koszozoltan/HGA22/docs/20260207_133258.jpg

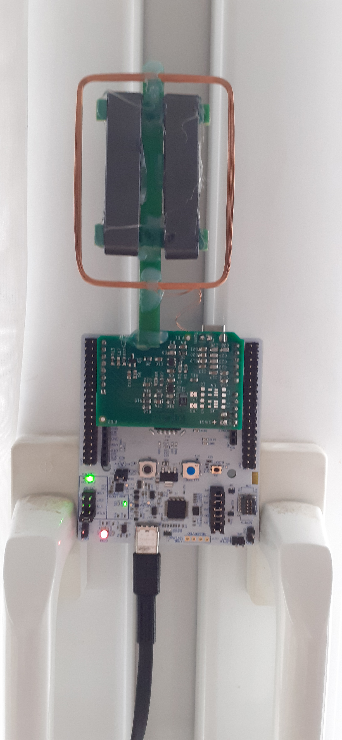
docs/20260207_133258.jpg
