koszozoltan/HGA22/docs/20260227_095823.jpg

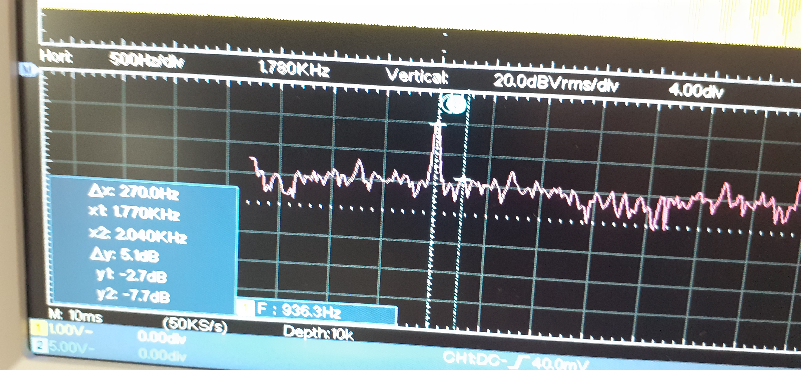
docs/20260227_095823.jpg
