koszozoltan/HGA22/docs/20260227_095835.jpg

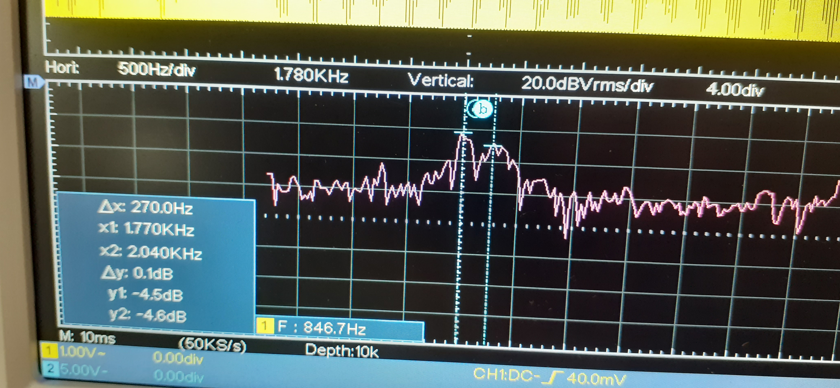
docs/20260227_095835.jpg
