koszozoltan/HGA22/docs/20260306_155042.jpg

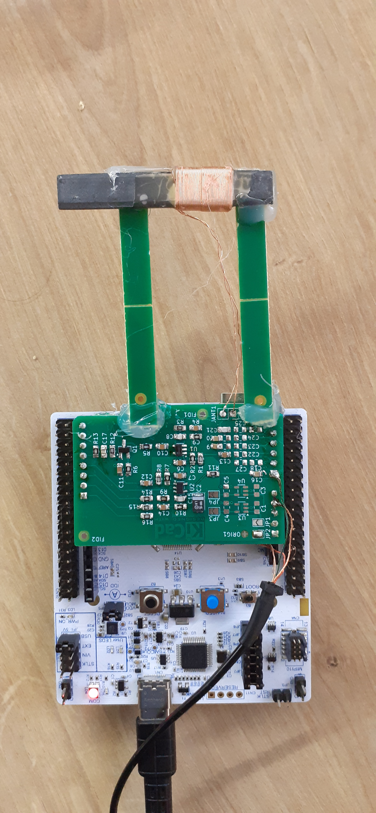
docs/20260306_155042.jpg
