koszozoltan/HGA22/hardware/v1.0/ltspice/HGA22_LM321LV_V2.asc

A1: modulate; mark=135.43kHz; space=135.77kHz
C1: cap; 4.2n
C2: cap; 100p
C3: cap; 100n
C4: cap; 100n
C5: cap; 100n
C6: cap; 100n
C7: cap; 100n
C8: cap; 100µ
C9: cap; 10p
C10: cap; 1n
C11: cap; 1n
C13: cap; 100n
L1: ind2; 320µ
L2: ind2; 320µ; Rser=0.1
M1: nmos; BSS138
R1: res; 1Meg
R2: res; 1Meg
R3: res; 1Meg
R4: res; 100
R5: res; 10G
R6: res; 1Meg
R7: res; 1k
R8: res; 10G
R9: res; 1Meg
R10: res; 100
R11: res; 1k
R12: res; 330k
R13: res; 100
R14: res; 1G
R15: res; 1k
R16: res; 1k
R17: res; 100k
U1: opamp2; LM321LV
U2: opamp2; LM321LV
V1: voltage; PULSE(0 1 0 10n 10n 5m 10m 3)
V2: voltage; PULSE(0 1 0 10n 10n 20m 30m 1)
V3: voltage; 5
V4: voltage; PULSE(0 3.3 0 30n 30n 3.5u 7.3u); Rser=10 Cpar=3p
Named nets: 0, A0
.tran 0 30m 0 10u
K L1 L2 0.00001
.inc LM321LV.cir
PULSE(0 3.3 0 30n 30n 3.5u 7.3u)
