koszozoltan/HGA22/firmware/v1.0/Sources/adc.c

/*
 * adc.c
 *
 *  Created on: Mar 5, 2026
 *      Author: development
 */

/* Includes ------------------------------------------------------------------*/

#include <string.h>
#include <math.h>
#include "util.h"
#include "queue.h"

#include "ringbuffer.h"
#include "tcp_server.h"
#include "arm_math.h"
#include "main.h"
#include "adc.h"




  #define ADC_CALIBRATION_TIMEOUT_MS       (   1UL)
  #define ADC_ENABLE_TIMEOUT_MS            (   1UL)
  #define ADC_DISABLE_TIMEOUT_MS           (   1UL)
  #define ADC_STOP_CONVERSION_TIMEOUT_MS   (   1UL)
  #define ADC_CONVERSION_TIMEOUT_MS        (4000UL)

  /* (CPU clock / ADC clock) is above 32.                                     */
  #define ADC_DELAY_CALIB_ENABLE_CPU_CYCLES  (LL_ADC_DELAY_CALIB_ENABLE_ADC_CYCLES * 32)

  /* supply Vdda (unit: mV).                                                  */
  #define VDDA_APPLI                       (3300UL)

  /* Init variable out of expected ADC conversion data range */
  #define VAR_CONVERTED_DATA_INIT_VALUE    (__LL_ADC_DIGITAL_SCALE(LL_ADC_RESOLUTION_12B) + 1)


  /* Time base range frequency maximum (unit: Hz).*/
  /* With a timer 16 bits, minimum frequency will be 1/32000 times this value.*/
  #define TIMER_FREQUENCY_RANGE_MAX_HZ    (32000UL)



__IO uint16_t uhADCxConvertedData[ADC_CONVERTED_DATA_BUFFER_SIZE];
__IO uint8_t ubDmaTransferStatus = 2U; /* Variable set into DMA interruption callback */
__IO uint8_t ubDmaTransferCnt= 0; /* Variable set into DMA interruption callback */

extern stream_q_t q_signal;

void ADC_Init(void) {

  uint32_t tmp_index;
/* Initialize ADC group regular data buffer values */
  for (tmp_index = 0; tmp_index < ADC_CONVERTED_DATA_BUFFER_SIZE; tmp_index++)
  {
    uhADCxConvertedData[tmp_index] = VAR_CONVERTED_DATA_INIT_VALUE;
  }

  /* USER CODE END 1 */

  /* MCU Configuration--------------------------------------------------------*/

  /* Reset of all peripherals, Initializes the Flash interface and the Systick. */
  LL_APB2_GRP1_EnableClock(LL_APB2_GRP1_PERIPH_SYSCFG);
  LL_APB1_GRP1_EnableClock(LL_APB1_GRP1_PERIPH_PWR);

  /* SysTick_IRQn interrupt configuration */
  NVIC_SetPriority(SysTick_IRQn, 3);


  /* Initialize all configured peripherals */
   //MX_GPIO_Init();
   MX_DMA_Init();
   MX_ADC1_Init();
   MX_TIM1_Init();
   /* USER CODE BEGIN 2 */

   /* Activate ADC */
   /* Perform ADC activation procedure to make it ready to convert. */
   ADC_Activate();

   /* Start ADC group regular conversion */
   /* Note: ADC conversion will effectively start at timer trigger event */
   /* Note: Hardware constraint (refer to description of the functions         */
   /*       below):                                                            */
   /*       On this STM32 series, setting of this feature is conditioned to    */
   /*       ADC state:                                                         */
   /*       ADC must be enabled without conversion on going on group regular,  */
   /*       without ADC disable command on going.                              */
   /* Note: In this example, all these checks are not necessary but are        */
   /*       implemented anyway to show the best practice usages                */
   /*       corresponding to reference manual procedure.                       */
   /*       Software can be optimized by removing some of these checks, if     */
   /*       they are not relevant considering previous settings and actions    */
   /*       in user application.                                               */
   if ((LL_ADC_IsEnabled(ADC1) == 1)               &&
       (LL_ADC_IsDisableOngoing(ADC1) == 0)        &&
       (LL_ADC_REG_IsConversionOngoing(ADC1) == 0)   )
   {
     LL_ADC_REG_StartConversion(ADC1);
   }
   else
   {
     /* Error: ADC conversion start could not be performed */
     Error_Handler();
   }

   /* Start time base */
   LL_TIM_EnableCounter(TIM1);


}


/**
  * @brief ADC1 Initialization Function
  * @param None
  * @retval None
  */
void MX_ADC1_Init(void) {

  LL_ADC_InitTypeDef ADC_InitStruct = {0};
  LL_ADC_REG_InitTypeDef ADC_REG_InitStruct = {0};

  LL_GPIO_InitTypeDef GPIO_InitStruct = {0};

  LL_RCC_SetADCClockSource(LL_RCC_ADC_CLKSOURCE_SYSCLK);

  /* Peripheral clock enable */
  LL_APB2_GRP1_EnableClock(LL_APB2_GRP1_PERIPH_ADC);

  LL_IOP_GRP1_EnableClock(LL_IOP_GRP1_PERIPH_GPIOA);
  /**ADC1 GPIO Configuration
  PA4   ------> ADC1_IN4
  */
  GPIO_InitStruct.Pin = LL_GPIO_PIN_0;
  GPIO_InitStruct.Mode = LL_GPIO_MODE_ANALOG;
  GPIO_InitStruct.Pull = LL_GPIO_PULL_NO;
  LL_GPIO_Init(GPIOA, &GPIO_InitStruct);

  /* ADC1 DMA Init */

  /* ADC1 Init */
  LL_DMA_SetPeriphRequest(DMA1, LL_DMA_CHANNEL_1, LL_DMAMUX_REQ_ADC1);

  LL_DMA_SetDataTransferDirection(DMA1, LL_DMA_CHANNEL_1, LL_DMA_DIRECTION_PERIPH_TO_MEMORY);

  LL_DMA_SetChannelPriorityLevel(DMA1, LL_DMA_CHANNEL_1, LL_DMA_PRIORITY_LOW);

  LL_DMA_SetMode(DMA1, LL_DMA_CHANNEL_1, LL_DMA_MODE_CIRCULAR);

  LL_DMA_SetPeriphIncMode(DMA1, LL_DMA_CHANNEL_1, LL_DMA_PERIPH_NOINCREMENT);

  LL_DMA_SetMemoryIncMode(DMA1, LL_DMA_CHANNEL_1, LL_DMA_MEMORY_INCREMENT);

  LL_DMA_SetPeriphSize(DMA1, LL_DMA_CHANNEL_1, LL_DMA_PDATAALIGN_HALFWORD);

  LL_DMA_SetMemorySize(DMA1, LL_DMA_CHANNEL_1, LL_DMA_MDATAALIGN_HALFWORD);

  /* ADC1 interrupt Init */
  NVIC_SetPriority(ADC1_IRQn, 0);
  NVIC_EnableIRQ(ADC1_IRQn);

  /* USER CODE BEGIN ADC1_Init 1 */
  /* Set DMA transfer addresses of source and destination */
  LL_DMA_ConfigAddresses(DMA1,
                         LL_DMA_CHANNEL_1,
                         LL_ADC_DMA_GetRegAddr(ADC1, LL_ADC_DMA_REG_REGULAR_DATA),
                         (uint32_t)&uhADCxConvertedData,
                         LL_DMA_DIRECTION_PERIPH_TO_MEMORY);

  /* Set DMA transfer size */
  LL_DMA_SetDataLength(DMA1,
                       LL_DMA_CHANNEL_1,
                       ADC_CONVERTED_DATA_BUFFER_SIZE);

  /* Enable DMA transfer interruption: transfer complete */
  LL_DMA_EnableIT_TC(DMA1,
                     LL_DMA_CHANNEL_1);

  /* Enable DMA transfer interruption: half transfer */
  LL_DMA_EnableIT_HT(DMA1,
                     LL_DMA_CHANNEL_1);

  /* Enable DMA transfer interruption: transfer error */
  LL_DMA_EnableIT_TE(DMA1,
                     LL_DMA_CHANNEL_1);

  /* Enable the DMA transfer */
  LL_DMA_EnableChannel(DMA1,
                       LL_DMA_CHANNEL_1);
  /* USER CODE END ADC1_Init 1 */

  /** Configure the global features of the ADC (Clock, Resolution, Data Alignment and number of conversion)
  */

   #define ADC_CHANNEL_CONF_RDY_TIMEOUT_MS ( 1U)
   #if (USE_TIMEOUT == 1)
   uint32_t Timeout ; /* Variable used for Timeout management */
   #endif /* USE_TIMEOUT */

  ADC_InitStruct.Clock = LL_ADC_CLOCK_SYNC_PCLK_DIV4;

  ADC_InitStruct.Resolution = LL_ADC_RESOLUTION_12B;
  ADC_InitStruct.DataAlignment = LL_ADC_DATA_ALIGN_RIGHT;
  ADC_InitStruct.LowPowerMode = LL_ADC_LP_MODE_NONE;
  LL_ADC_Init(ADC1, &ADC_InitStruct);
  LL_ADC_REG_SetSequencerConfigurable(ADC1, LL_ADC_REG_SEQ_FIXED);
  ADC_REG_InitStruct.TriggerSource = LL_ADC_REG_TRIG_EXT_TIM1_TRGO2;
  ADC_REG_InitStruct.SequencerLength = LL_ADC_REG_SEQ_SCAN_DISABLE;
  ADC_REG_InitStruct.SequencerDiscont = LL_ADC_REG_SEQ_DISCONT_DISABLE;
  ADC_REG_InitStruct.ContinuousMode = LL_ADC_REG_CONV_SINGLE;
  ADC_REG_InitStruct.DMATransfer = LL_ADC_REG_DMA_TRANSFER_UNLIMITED;
  ADC_REG_InitStruct.Overrun = LL_ADC_REG_OVR_DATA_OVERWRITTEN;
  LL_ADC_REG_Init(ADC1, &ADC_REG_InitStruct);
  LL_ADC_REG_SetSequencerScanDirection(ADC1, LL_ADC_REG_SEQ_SCAN_DIR_FORWARD);
#warning ADC oversample
#if 0
  LL_ADC_SetOverSamplingScope(ADC1, LL_ADC_OVS_DISABLE);
#else
  LL_ADC_SetOverSamplingScope(ADC1, LL_ADC_OVS_GRP_REGULAR_CONTINUED);
   LL_ADC_ConfigOverSamplingRatioShift(ADC1, LL_ADC_OVS_RATIO_32, LL_ADC_OVS_SHIFT_RIGHT_5);
   LL_ADC_SetOverSamplingDiscont(ADC1, LL_ADC_OVS_REG_CONT);
#endif


  LL_ADC_SetTriggerFrequencyMode(ADC1, LL_ADC_CLOCK_FREQ_MODE_HIGH);
  LL_ADC_REG_SetSequencerChAdd(ADC1, LL_ADC_CHANNEL_0);

   /* Poll for ADC channel configuration ready */
   #if (USE_TIMEOUT == 1)
   Timeout = ADC_CHANNEL_CONF_RDY_TIMEOUT_MS;
   #endif /* USE_TIMEOUT */
   while (LL_ADC_IsActiveFlag_CCRDY(ADC1) == 0)
     {
   #if (USE_TIMEOUT == 1)
   /* Check Systick counter flag to decrement the time-out value */
   if (LL_SYSTICK_IsActiveCounterFlag())
     {
   if(Timeout-- == 0)
         {
   Error_Handler();
         }
     }
   #endif /* USE_TIMEOUT */
     }
   /* Clear flag ADC channel configuration ready */
   LL_ADC_ClearFlag_CCRDY(ADC1);
  LL_ADC_REG_SetTriggerEdge(ADC1, LL_ADC_REG_TRIG_EXT_RISING);
#warning ADC oversample
#if 0
  LL_ADC_SetSamplingTimeCommonChannels(ADC1, LL_ADC_SAMPLINGTIME_COMMON_1, LL_ADC_SAMPLINGTIME_79CYCLES_5);
#else
  LL_ADC_SetSamplingTimeCommonChannels(ADC1, LL_ADC_SAMPLINGTIME_COMMON_1, LL_ADC_SAMPLINGTIME_7CYCLES_5);
#endif

  LL_ADC_DisableIT_EOC(ADC1);
  LL_ADC_DisableIT_EOS(ADC1);

   /* Enable ADC internal voltage regulator */
   LL_ADC_EnableInternalRegulator(ADC1);
   /* Delay for ADC internal voltage regulator stabilization. */
   /* Compute number of CPU cycles to wait for, from delay in us. */
   /* Note: Variable divided by 2 to compensate partially */
   /* CPU processing cycles (depends on compilation optimization). */
   /* Note: If system core clock frequency is below 200kHz, wait time */
   /* is only a few CPU processing cycles. */
   uint32_t wait_loop_index;
   wait_loop_index = ((LL_ADC_DELAY_INTERNAL_REGUL_STAB_US * (SystemCoreClock / (100000 * 2))) / 10);
   while(wait_loop_index != 0)
     {
   wait_loop_index--;
     }
  /* USER CODE BEGIN ADC1_Init 2 */

  /* Configuration of ADC interruptions */
  /* Enable interruption ADC group regular overrun */
  LL_ADC_EnableIT_OVR(ADC1);

  /* USER CODE END ADC1_Init 2 */

}

/**
  * @brief TIM1 Initialization Function
  * @param None
  * @retval None
  */
void MX_TIM1_Init(void) {

  /* USER CODE BEGIN TIM1_Init 0 */
  uint32_t tim_prescaler;
  uint32_t tim_period;
  /* USER CODE END TIM1_Init 0 */

  LL_TIM_InitTypeDef TIM_InitStruct = {0};

  /* Peripheral clock enable */
  LL_APB2_GRP1_EnableClock(LL_APB2_GRP1_PERIPH_TIM1);

  /* USER CODE BEGIN TIM1_Init 1 */

  /* Set timer prescaler value (timer frequency) */
  /* Note: Value TIMER_FREQUENCY_RANGE_MAX_HZ with factor 2 to have a minimum
           timer resolution */
  tim_prescaler = __LL_TIM_CALC_PSC(SystemCoreClock, TIMER_FREQUENCY_RANGE_MAX_HZ * 2);

  /* Set timer period value (time base frequency) */
  tim_period = __LL_TIM_CALC_ARR(SystemCoreClock, tim_prescaler, TIMER_FREQUENCY_HZ);

  /* USER CODE END TIM1_Init 1 */
  TIM_InitStruct.Prescaler = tim_prescaler;
  TIM_InitStruct.CounterMode = LL_TIM_COUNTERMODE_UP;
  TIM_InitStruct.Autoreload = tim_period;
  TIM_InitStruct.ClockDivision = LL_TIM_CLOCKDIVISION_DIV1;
  TIM_InitStruct.RepetitionCounter = 0;
  LL_TIM_Init(TIM1, &TIM_InitStruct);
  LL_TIM_DisableARRPreload(TIM1);
  LL_TIM_SetClockSource(TIM1, LL_TIM_CLOCKSOURCE_INTERNAL);
  LL_TIM_SetTriggerOutput(TIM1, LL_TIM_TRGO_UPDATE);
  LL_TIM_SetTriggerOutput2(TIM1, LL_TIM_TRGO2_UPDATE);
  LL_TIM_DisableMasterSlaveMode(TIM1);
}

/**
  * Enable DMA controller clock
  */
void MX_DMA_Init(void) {

  /* Init with LL driver */
  /* DMA controller clock enable */
  LL_AHB1_GRP1_EnableClock(LL_AHB1_GRP1_PERIPH_DMA1);

  /* DMA interrupt init */
  /* DMA1_Channel1_IRQn interrupt configuration */
  NVIC_SetPriority(DMA1_Channel1_IRQn, 0);
  NVIC_EnableIRQ(DMA1_Channel1_IRQn);

}

void ADC_Activate(void) {
  __IO uint32_t wait_loop_index = 0U;
  __IO uint32_t backup_setting_adc_dma_transfer = 0U;
  #if (USE_TIMEOUT == 1)
  uint32_t Timeout = 0U; /* Variable used for timeout management */
  #endif /* USE_TIMEOUT */

  /*## Operation on ADC hierarchical scope: ADC instance #####################*/

  /* Note: Hardware constraint (refer to description of the functions         */
  /*       below):                                                            */
  /*       On this STM32 series, setting of these features is conditioned to  */
  /*       ADC state:                                                         */
  /*       ADC must be disabled.                                              */
  /* Note: In this example, all these checks are not necessary but are        */
  /*       implemented anyway to show the best practice usages                */
  /*       corresponding to reference manual procedure.                       */
  /*       Software can be optimized by removing some of these checks, if     */
  /*       they are not relevant considering previous settings and actions    */
  /*       in user application.                                               */
  if (LL_ADC_IsEnabled(ADC1) == 0)
  {
    /* Enable ADC internal voltage regulator */
    LL_ADC_EnableInternalRegulator(ADC1);

    /* Delay for ADC internal voltage regulator stabilization.                */
    /* Compute number of CPU cycles to wait for, from delay in us.            */
    /* Note: Variable divided by 2 to compensate partially                    */
    /*       CPU processing cycles (depends on compilation optimization).     */
    /* Note: If system core clock frequency is below 200kHz, wait time        */
    /*       is only a few CPU processing cycles.                             */
    wait_loop_index = ((LL_ADC_DELAY_INTERNAL_REGUL_STAB_US * (SystemCoreClock / (100000 * 2))) / 10);
    while(wait_loop_index != 0)
    {
      wait_loop_index--;
    }

    /* Disable ADC DMA transfer request during calibration */
    /* Note: Specificity of this STM32 series: Calibration factor is           */
    /*       available in data register and also transferred by DMA.           */
    /*       To not insert ADC calibration factor among ADC conversion data   */
    /*       in DMA destination address, DMA transfer must be disabled during */
    /*       calibration.                                                     */
    backup_setting_adc_dma_transfer = LL_ADC_REG_GetDMATransfer(ADC1);
    LL_ADC_REG_SetDMATransfer(ADC1, LL_ADC_REG_DMA_TRANSFER_NONE);

    /* Run ADC self calibration */
    LL_ADC_StartCalibration(ADC1);

    /* Poll for ADC effectively calibrated */
    #if (USE_TIMEOUT == 1)
    Timeout = ADC_CALIBRATION_TIMEOUT_MS;
    #endif /* USE_TIMEOUT */

    while (LL_ADC_IsCalibrationOnGoing(ADC1) != 0)
    {
    #if (USE_TIMEOUT == 1)
      /* Check Systick counter flag to decrement the time-out value */
      if (LL_SYSTICK_IsActiveCounterFlag())
      {
        if(Timeout-- == 0)
        {
          /* Error: Time-out */
          Error_Handler();
        }
      }
    #endif /* USE_TIMEOUT */
    }

    /* Restore ADC DMA transfer request after calibration */
    LL_ADC_REG_SetDMATransfer(ADC1, backup_setting_adc_dma_transfer);

    /* Delay between ADC end of calibration and ADC enable.                   */
    /* Note: Variable divided by 2 to compensate partially                    */
    /*       CPU processing cycles (depends on compilation optimization).     */
    wait_loop_index = (ADC_DELAY_CALIB_ENABLE_CPU_CYCLES >> 1);
    while(wait_loop_index != 0)
    {
      wait_loop_index--;
    }

    /* Enable ADC */
    LL_ADC_Enable(ADC1);

    /* Poll for ADC ready to convert */
    #if (USE_TIMEOUT == 1)
    Timeout = ADC_ENABLE_TIMEOUT_MS;
    #endif /* USE_TIMEOUT */

    while (LL_ADC_IsActiveFlag_ADRDY(ADC1) == 0)
    {
    #if (USE_TIMEOUT == 1)
      /* Check Systick counter flag to decrement the time-out value */
      if (LL_SYSTICK_IsActiveCounterFlag())
      {
        if(Timeout-- == 0)
        {
          /* Error: Time-out */
          Error_Handler();
        }
      }
    #endif /* USE_TIMEOUT */
    }

    /* Note: ADC flag ADRDY is not cleared here to be able to check ADC       */
    /*       status afterwards.                                               */
    /*       This flag should be cleared at ADC Deactivation, before a new    */
    /*       ADC activation, using function "LL_ADC_ClearFlag_ADRDY()".       */
  }

  /*## Operation on ADC hierarchical scope: ADC group regular ################*/
  /* Note: No operation on ADC group regular performed here.                  */
  /*       ADC group regular conversions to be performed after this function  */
  /*       using function:                                                    */
  /*       "LL_ADC_REG_StartConversion();"                                    */

  /*## Operation on ADC hierarchical scope: ADC group injected ###############*/
  /* Note: Feature not available on this STM32 series */

}


void AdcDmaTransferComplete_Callback() {


	sq_push(&q_signal, (int16_t *)uhADCxConvertedData, ADC_CONVERTED_DATA_BUFFER_SIZE);

	ubDmaTransferStatus = 1;
	ubDmaTransferCnt++;
}


/**
  * @brief  DMA half transfer callback
  * @note   This function is executed when the half transfer interrupt
  *         is generated
  * @retval None
  */
void AdcDmaTransferHalf_Callback() {

}



/**
  * @brief  DMA transfer error callback
  * @note   This function is executed when the transfer error interrupt
  *         is generated during DMA transfer
  * @retval None
  */
void AdcDmaTransferError_Callback() {
  if(ubDmaTransferStatus == 1)
  {
    /* Update status variable of DMA transfer */
    ubDmaTransferStatus = 0;
  }

  /* Error detected during DMA transfer */
  Error_Handler();
}

/**
  * @brief  ADC group regular overrun interruption callback
  * @note   This function is executed when ADC group regular
  *         overrun error occurs.
  * @retval None
  */
void AdcGrpRegularOverrunError_Callback(void) {
  /* Note: Disable ADC interruption that caused this error before entering in
           infinite loop below. */

  /* In case of error due to overrun: Disable ADC group regular overrun interruption */
  LL_ADC_DisableIT_OVR(ADC1);

  /* Error reporting */
  Error_Handler();
}
