koszozoltan/HGA22/firmware/v1.0/Sources/iq.c

#include "main.h"
#include <string.h>
#include "math.h"
#include "iq.h"
#include "util.h"


static const  int16_t sinTable[TABLE_SIZE] = {
0,
201,402,603,804,1005,1206,1407,1607,1808,2009,2210,2410,2611,2811,3011,3211,
3411,3611,3811,4011,4210,4409,4609,4808,5006,5205,5403,5602,5800,5997,6195,6392,
6589,6786,6983,7179,7375,7571,7766,7961,8156,8351,8545,8739,8933,9126,9319,9512,
9704,9896,10087,10278,10469,10659,10849,11039,11228,11416,11605,11793,11980,12167,12353,12539,
12725,12910,13094,13278,13462,13645,13828,14010,14191,14372,14552,14732,14912,15090,15269,15446,
15623,15800,15976,16151,16325,16499,16673,16846,17018,17189,17360,17530,17700,17869,18037,18204,
18371,18537,18703,18868,19032,19195,19358,19519,19681,19841,20001,20159,20318,20475,20631,20787,
20942,21097,21250,21403,21555,21706,21856,22005,22154,22301,22448,22594,22740,22884,23027,23170,
23312,23453,23593,23732,23870,24007,24144,24279,24414,24547,24680,24812,24943,25073,25201,25330,
25457,25583,25708,25832,25955,26077,26199,26319,26438,26557,26674,26790,26905,27020,27133,27245,
27356,27466,27576,27684,27791,27897,28002,28106,28208,28310,28411,28511,28609,28707,28803,28898,
28993,29086,29178,29269,29359,29447,29535,29621,29707,29791,29874,29956,30037,30117,30196,30273,
30350,30425,30499,30572,30644,30714,30784,30852,30919,30985,31050,31114,31176,31237,31298,31357,
31414,31471,31526,31581,31634,31685,31736,31785,31834,31881,31927,31971,32015,32057,32098,32138,
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
    if (x <= -1.0f) return -32768;
    return (int32_t)(x * Q15_SCALE);
}

void iq_st_init(iq_st *iq, uint16_t mixFreq)
{
    iq->phase  = 0;
    iq->i_filt = 0;
    iq->q_filt = 0;
    iq->prev_i = 0;
    iq->prev_q = 0;

    iq->sampleRate = 8000;
    iq->mixFreq    = mixFreq;

    // keresés a táblában
    for (int i = 0; i < (int)(sizeof(mix_table)/sizeof(mix_table[0])); i++)
    {
        if (mix_table[i].freq == mixFreq)
        {
            iq->omega    = mix_table[i].omega_q15;
            iq->lpfAlpha = mix_table[i].alpha_q15;
            return;
        }
    }

    // ha nincs egyezés: safe default
    iq->omega    = 0;
    iq->lpfAlpha = 0;
}


// ---------------------------
//   Sin/Cos táblázat (Q15)
// ---------------------------
void initSinCosTable(void) {
#if 0
    for (int i = 0; i < TABLE_SIZE; i++)
    {
        float angle = (2.0f * PI * i) / TABLE_SIZE;
        sinTable[i] = float_to_q15(sinf(angle));
        cosTable[i] = float_to_q15(cosf(angle));
    }
#endif
}

// ---------------------------
//  Fázis → index (Q15)
//  phase = rad * 32768
// ---------------------------
static inline int phaseToIndex(int32_t phase_q15)
{
    // skála: TABLE_SIZE / (2π)  →  1024 / 6.283185
    // állandó Q15-ben:
    const float scale = (float)TABLE_SIZE / (2.0f * PI);
    int32_t scaled = (int32_t)(phase_q15 / 32768.0f * scale);

    int idx = scaled % TABLE_SIZE;
    if (idx < 0) idx += TABLE_SIZE;
    return idx;
}

// ---------------------------
//       IQ Power Q15
// ---------------------------
int32_t iq_power_q15(int16_t sample, iq_st* st)
{


    int idx = phaseToIndex(st->phase);

    int16_t lo_i = cosTable[idx];
    int16_t lo_q = sinTable[idx];

    // fázis növelés
    st->phase += st->omega;
    static const int32_t FULL_ROT = (int32_t)(2.0f * PI * 32768);
    if (st->phase >= FULL_ROT) st->phase -= FULL_ROT;
    else if (st->phase < 0)   st->phase += FULL_ROT;

    // I/Q keverés: (sample * lo) >> 15
    int32_t i = ( (int32_t)sample * lo_i ) >> 15;
    int32_t q = ( (int32_t)sample * lo_q ) >> 15;

    // LPF: y += α (x − y)
    st->i_filt += ( (int32_t)st->lpfAlpha * (i - st->i_filt) ) >> 15;
    st->q_filt += ( (int32_t)st->lpfAlpha * (q - st->q_filt) ) >> 15;

    // power = I^2 + Q^2   (>>15, hogy normalizált legyen)
    int32_t power =
        ((st->i_filt * st->i_filt) >> 15) +
        ((st->q_filt * st->q_filt) >> 15);

    return power;
}

int16_t scale_to_x15_int(int32_t x, int32_t min, int32_t max, int64_t range ) {
    if (x <= min) return -32768;
    if (x >= max) return 32767;
    int64_t result = (((int64_t)(x - min) << 16) / range) - 32768;

    return (int16_t)result;
}
